having11/Connector-X/connector_x/include/Patterns.h

#pragma once

#include <Adafruit_GFX.h>
#include <FastLED_NeoMatrix.h>
#include <FastLED.h>
#include <LittleFS.h>

#include "Constants.h"
#include "Configuration.h"
#include "SpectrumAnalyzer.h"

#include <math.h>

/**
 * Will be called after set delay has passed
 * @param state resets to 0 after current state >= numStates
 * @returns true if LEDs should show
 */
typedef bool (*ExecutePatternCallback)(CRGB *strip, uint32_t color,
                                       uint16_t state, uint16_t ledCount);

enum class PatternType
{
    None = 0,
    SetAll = 1,
    Blink = 2,
    RGBFade = 3,
    HackerMode = 4,
    Breathing = 5,
    SineRoll = 6,
    Chase = 7,
    AngryEyes = 8,
    HappyEyes = 9,
    BlinkingEyes = 10,
    SurprisedEyes = 11,
    Amogus = 12,
    Spectrum = 13,
    OwOEyes = 14,
};

enum class PatternStateMode
{
    Constant = 0,
    // When set as the mode, will add the numStates value to ledCount
    LedCount,
};

struct Pattern
{
    PatternType type;
    PatternStateMode mode;
    uint16_t numStates;
    uint16_t changeDelayDefault;
    ExecutePatternCallback cb;
};

struct bmp_file_header_t {
  uint16_t signature;
  uint32_t file_size;
  uint16_t reserved[2];
  uint32_t image_offset;
};

struct bmp_image_header_t {
  uint32_t header_size;
  uint32_t image_width;
  uint32_t image_height;
  uint16_t color_planes;
  uint16_t bits_per_pixel;
  uint32_t compression_method;
  uint32_t image_size;
  uint32_t horizontal_resolution;
  uint32_t vertical_resolution;
  uint32_t colors_in_palette;
  uint32_t important_colors;
};

static uint16_t read16(File &file) {
    uint8_t buf[2];

    file.readBytes((char*)buf, sizeof(uint16_t));

    return (buf[1] << 8) | (buf[0] << 0);
}

static uint32_t read32(File &file) {
    uint8_t buf[4];

    file.readBytes((char*)buf, sizeof(uint32_t));

    return (buf[3] << 24) | (buf[2] << 16) | (buf[1] << 8) | (buf[0] << 0);
}

// Call delete[] on the returned value after done using
static uint8_t* getBitmapBytes(String filePath) {
    File file = LittleFS.open(filePath, "r");
    // Serial.printf("Pos=%lu\n", file.position());

    for (uint32_t i = 0; i < 56; i++) {
        uint8_t val;
        file.readBytes((char*)&val, sizeof(uint8_t));
        // Serial.printf("%X ", val);
    }

    Serial.println();
    file.seek(0);

    bmp_file_header_t fileHeader;
    fileHeader.signature = read16(file);
    fileHeader.file_size = read32(file);
    fileHeader.reserved[0] = read16(file);
    fileHeader.reserved[1] = read16(file);
    fileHeader.image_offset = read32(file);
    // Serial.printf("File size=%lu\n", fileHeader.file_size);
    bmp_image_header_t imageHeader;
    file.readBytes((char*)&imageHeader, sizeof(imageHeader));
    // Serial.printf("Pos=%lu\n", file.position());

    // Serial.printf("Bmp bpp=%d W=%d H=%d\n",
    //     imageHeader.bits_per_pixel, imageHeader.image_width, imageHeader.image_height);

    if (imageHeader.bits_per_pixel == 16) {
        // Serial.printf("Offset=%lu\n", fileHeader.image_offset);
        file.seek(fileHeader.image_offset);
        uint32_t totalSize = imageHeader.image_width * imageHeader.image_height * (imageHeader.bits_per_pixel / 8);
        Serial.printf("Found good bmp with total size=%d\n", totalSize);
        uint8_t* bytes = new uint8_t[totalSize];
        file.readBytes((char*)bytes, totalSize);
        // Serial.printf("Pos=%lu\n", file.position());

        file.close();
        return bytes;
    }

    file.close();
    return nullptr;
}

static bool writeToMatrix(CRGB *strip, uint16_t state, String filePathPrefix, uint16_t ledCount)
{
    FastLED_NeoMatrix *matrix = new FastLED_NeoMatrix(strip, configuration.led1.matrix.width,
        configuration.led1.matrix.height, configuration.led1.matrix.flags);
    if (ledCount != matrix->width() * matrix->height()) {
        delete matrix;
        return false;
    }

    String filePath = filePathPrefix + String(state) + String(".bmp");
    uint8_t* bytes = getBitmapBytes(filePath);

    if (bytes) {
        matrix->drawRGBBitmap(0, 0, (uint16_t*)bytes, matrix->width(), matrix->height());
        delete[] bytes;
    }
    
    delete matrix;
    return true;
}

static void setColorScaled(CRGB *strip, uint16_t ledNumber, byte red, byte green, byte blue, byte scaling)
{
    // Scale RGB with a common brightness parameter
    strip[ledNumber] = CRGB((red * scaling) >> 8, (green * scaling) >> 8, (blue * scaling) >> 8);
}

static void setColorScaled(CRGB *strip, uint16_t ledNumber, uint32_t color, byte scaling)
{
    setColorScaled(strip, ledNumber, color >> 16, (color >> 8) & 0xff, color & 0xff, scaling & 0xff);
}

namespace Animation
{
    static inline uint32_t Wheel(uint8_t position)
    {
        position = 255 - position;

        if (position < 85)
        {
            return (uint32_t)CRGB(255 - position * 3, 0, position * 3);
        }

        if (position < 170)
        {
            position -= 85;
            return (uint32_t)CRGB(0, position * 3, 255 - position * 3);
        }

        position -= 170;
        return (uint32_t)CRGB(position * 3, 255 - position * 3, 0);
    }
    // The function signature comes from ExecutePatternCallback in Patterns.h

    static bool executePatternNone(CRGB *strip, uint32_t color,
                                   uint16_t state, uint16_t ledCount)
    {
        return false;
    }

    static bool executePatternSetAll(CRGB *strip, uint32_t color,
                                     uint16_t state, uint16_t ledCount)
    {
        for (size_t i = 0; i < ledCount; i++)
        {
            strip[i] = color;
        }

        return true;
    }

    static bool executePatternBlink(CRGB *strip, uint32_t color,
                                    uint16_t state, uint16_t ledCount)
    {
        switch (state)
        {
        case 0:
            for (size_t i = 0; i < ledCount; i++)
            {
                strip[i] = color;
            }
            return true;

        case 1:
            for (size_t i = 0; i < ledCount; i++)
            {
                strip[i] = 0;
            }
            return true;

        default:
            return false;
        }
    }

    static bool executePatternRGBFade(CRGB *strip, uint32_t color,
                                      uint16_t state, uint16_t ledCount)
    {
        for (size_t i = 0; i < ledCount; i++)
        {
            strip[i] = Wheel(((i * 256 / ledCount) + state) & 255);
        }
        return true;
    }

    static bool executePatternHackerMode(CRGB *strip, uint32_t color,
                                         uint16_t state, uint16_t ledCount)
    {
        switch (state)
        {
        case 0:
            return executePatternSetAll(strip, (uint32_t)CRGB(0, 200, 0), 0,
                                        ledCount);

        case 1:
            return executePatternSetAll(strip, (uint32_t)CRGB(5, 100, 5), 0,
                                        ledCount);

        default:
            return false;
        }
    }

    static bool executePatternBreathing(CRGB *strip, uint32_t color,
                                        uint16_t state, uint16_t ledCount)
    {
        if (state > 255)
        {
            state = 511 - state;
        }
        for (size_t i = 0; i < ledCount; i++)
        {
            setColorScaled(strip, i, color, state & 0xff);
        }

        return true;
    }

    static bool executePatternSineRoll(CRGB *strip, uint32_t color,
                                        uint16_t state, uint16_t ledCount)
    {
        for (uint16_t index = 0; index < ledCount; index++)
        {
            double t1 = (2 * M_PI / sineRollStates) * (sineRollStates - state);
            double t2 = (1 / sineRollWidth) * M_PI * index;
            double brightness = sin(t2 + t1) + 1;
            // Truncate all values < 0 to 0
            uint8_t quantizedBrightness = 255 * (brightness / 2);
            setColorScaled(strip, index, color, quantizedBrightness);
        }

        return true;
    }

    static bool executePatternChase(CRGB *strip, uint32_t color,
                                        uint16_t state, uint16_t ledCount)
    {
        uint16_t startState = chaseWidth;
        uint16_t endState = (ledCount + chaseWidth) - 1;
        uint16_t startIndex = state;
        uint16_t endIndex = (state + chaseWidth) - 1;

        for (uint16_t index = startState; index <= endState; index++)
        {
            if (index >= startIndex && index <= endIndex)
            {
                strip[index - startState] = color;
            }
        }

        return true;
    }

    static bool executePatternAngryEyes(CRGB *strip, uint32_t color,
                                        uint16_t state, uint16_t ledCount)
    {
        return writeToMatrix(strip, state, "/angry_eyes/", ledCount);
    }

    static bool executePatternHappyEyes(CRGB *strip, uint32_t color,
                                        uint16_t state, uint16_t ledCount)
    {
        return writeToMatrix(strip, state, "/happy_eyes/", ledCount);
    }
                                    
    static bool executePatternBlinkingEyes(CRGB *strip, uint32_t color,
                                        uint16_t state, uint16_t ledCount)
    {
        return writeToMatrix(strip, state, "/blinking_eyes/", ledCount);
    }

    static bool executePatternSurprisedEyes(CRGB *strip, uint32_t color,
                                        uint16_t state, uint16_t ledCount)
    {
        return writeToMatrix(strip, state, "/surprised_eyes/", ledCount);
    }

    static bool executePatternAmogus(CRGB *strip, uint32_t color,
                                        uint16_t state, uint16_t ledCount)
    {
        return writeToMatrix(strip, state, "/amogus/", ledCount);
    }

    static bool executePatternOwOEyes(CRGB *strip, uint32_t color,
                                        uint16_t state, uint16_t ledCount)
    {
        return writeToMatrix(strip, state, "/owo_eyes/", ledCount);
    }

    static bool executePatternSpectrum(CRGB *strip, uint32_t color,
                                        uint16_t state, uint16_t ledCount)
    {
        uint16_t sampleCount = spectrum.sampleCount();
        float *bins = nullptr;

        bool entered = mutex_enter_timeout_us(&spectrumMtx, 20);
        if (entered)
        {
            Serial.printf("In bins\n");
            bins = new float[sampleCount];
            memcpy(bins, spectrum.bins(), sampleCount);
            mutex_exit(&spectrumMtx);
        }

        if (bins)
        {
            Serial.printf("Got bins\n");
            FastLED_NeoMatrix *matrix = new FastLED_NeoMatrix(strip, configuration.led1.matrix.width,
                configuration.led1.matrix.height, configuration.led1.matrix.flags);
            if (ledCount != matrix->width() * matrix->height()) {
                delete matrix;
                return false;
            }

            for (uint16_t col = 0; col < matrix->width(); col++)
            {
                Serial.printf("Col=%d | height=%f\n", col, matrix->height() * bins[col]);
                matrix->drawFastVLine(col, 0, matrix->height() * bins[col], matrix->Color24to16(color));
            }

            delete matrix;
            delete[] bins;
        }

        return true;
    }

    // ! The order of these MUST match the order in PatternType !
    static Pattern patterns[PatternCount] = {
        {.type = PatternType::None,
         .mode = PatternStateMode::Constant,
         .numStates = 0,
         .changeDelayDefault = 0,
         .cb = Animation::executePatternNone},
        {.type = PatternType::SetAll,
         .mode = PatternStateMode::Constant,
         .numStates = 1,
         .changeDelayDefault = 500u,
         .cb = Animation::executePatternSetAll},
        {.type = PatternType::Blink,
         .mode = PatternStateMode::Constant,
         .numStates = 2,
         .changeDelayDefault = 400u,
         .cb = Animation::executePatternBlink},
        {.type = PatternType::RGBFade,
         .mode = PatternStateMode::Constant,
         .numStates = 256,
         .changeDelayDefault = 10u,
         .cb = Animation::executePatternRGBFade},
        {.type = PatternType::HackerMode,
         .mode = PatternStateMode::Constant,
         .numStates = 2,
         .changeDelayDefault = 100u,
         .cb = Animation::executePatternHackerMode},
        {.type = PatternType::Breathing,
         .mode = PatternStateMode::Constant,
         .numStates = 512u,
         .changeDelayDefault = 5,
         .cb = Animation::executePatternBreathing},
        {.type = PatternType::SineRoll,
         .mode = PatternStateMode::Constant,
         .numStates = sineRollStates,
         .changeDelayDefault = 5,
         .cb = Animation::executePatternSineRoll},
        {.type = PatternType::Chase,
         .mode = PatternStateMode::LedCount,
         .numStates = chaseWidth,
         .changeDelayDefault = 20,
         .cb = Animation::executePatternChase},
        {.type = PatternType::AngryEyes,
         .mode = PatternStateMode::Constant,
         .numStates = 5,
         .changeDelayDefault = 1000,
         .cb = Animation::executePatternAngryEyes},
        {.type = PatternType::HappyEyes,
         .mode = PatternStateMode::Constant,
         .numStates = 3,
         .changeDelayDefault = 1000,
         .cb = Animation::executePatternHappyEyes},
        {.type = PatternType::BlinkingEyes,
         .mode = PatternStateMode::Constant,
         .numStates = 5,
         .changeDelayDefault = 1000,
         .cb = Animation::executePatternBlinkingEyes},
        {.type = PatternType::SurprisedEyes,
         .mode = PatternStateMode::Constant,
         .numStates = 1,
         .changeDelayDefault = 1000,
         .cb = Animation::executePatternSurprisedEyes},
         {.type = PatternType::Amogus,
         .mode = PatternStateMode::Constant,
         .numStates = 41,
         .changeDelayDefault = 125,
         .cb = Animation::executePatternAmogus},
         {.type = PatternType::Spectrum,
         .mode = PatternStateMode::Constant,
         .numStates = 1,
         .changeDelayDefault = 50,
         .cb = Animation::executePatternSpectrum},
         {.type = PatternType::OwOEyes,
         .mode = PatternStateMode::Constant,
         .numStates = 7,
         .changeDelayDefault = 750,
         .cb = Animation::executePatternOwOEyes},
    };
} // namespace Animation
