having11/Connector-X/connector_x/include/SpectrumAnalyzer.h

#pragma once

#include <Arduino.h>
#include <arduinoFFT.h>

#include <memory>

#include <pico/stdlib.h>
#include <hardware/adc.h>
#include <hardware/dma.h>

#include "Constants.h"

class SpectrumAnalyzer
{
  public:
    /**
     * @brief Construct a new Spectrum Analyzer object
     * 
     * @param irq Call dmaHandler in the function
     */
    SpectrumAnalyzer();
    ~SpectrumAnalyzer();
    void init(void);
    void startSampling(void);
    void dmaHandler(void);
    /**
     * @brief USE A MUTEX AROUND THIS
     * 
     */
    void update(void);
    uint16_t sampleCount(void) const;
    /**
     * @brief USE A MUTEX AROUND THIS
     * 
     * @return float* A pointer to the resulting FFT bins
     */
    float* bins() const;

  private:
    dma_channel_config cfg;
    uint dmaChannel;
    float *vReal;
    float *vImag;
    uint8_t *adcBuf;
    volatile bool hasData = false;
    std::unique_ptr<ArduinoFFT<float>> fft;
};

static mutex_t spectrumMtx;
static SpectrumAnalyzer spectrum{};
